omenmicro/pia-board/hw/photo/20181028_103724-1280.jpg

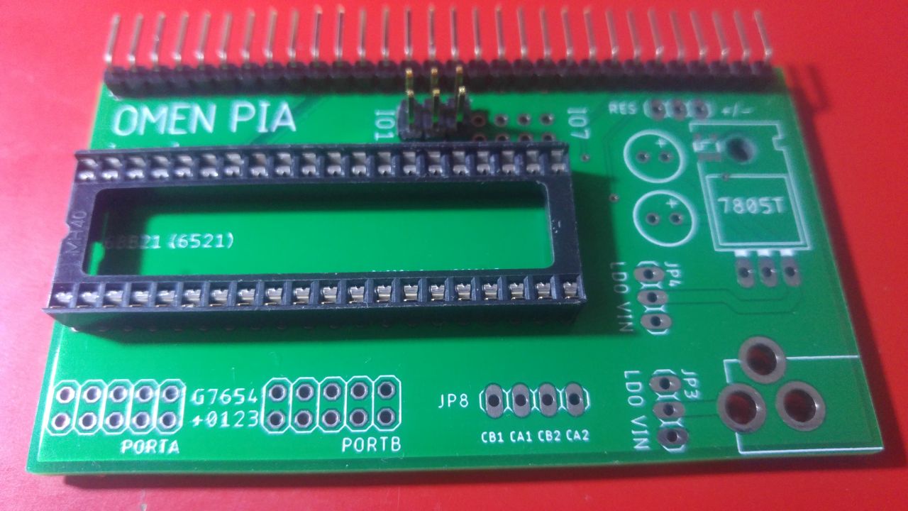
hw/photo/20181028_103724-1280.jpg
