omenmicro/pia-board/hw/photo/20181028_103731-1280.jpg

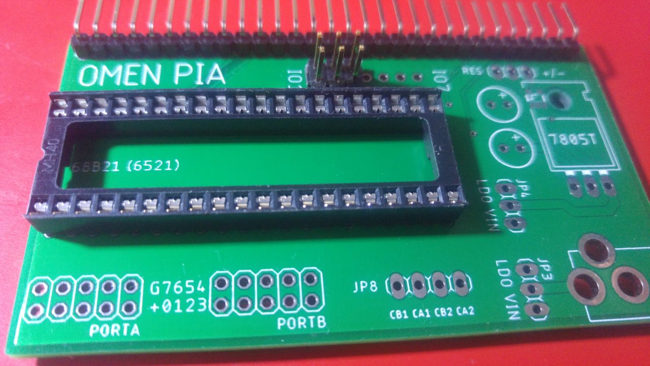
hw/photo/20181028_103731-1280.jpg
