omenmicro/pia-board/hw/photo/20181124_150051.jpg

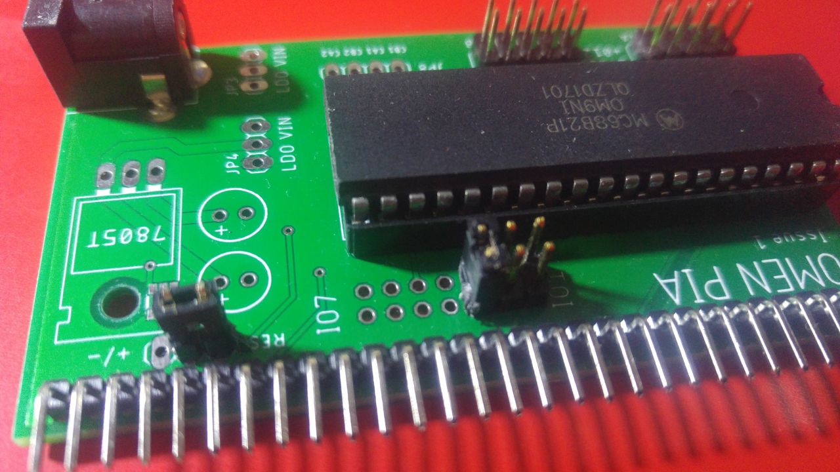
hw/photo/20181124_150051.jpg
